JoshuaMularczyk/Software_Defined_Radio_Receiver/Visuals/Arduino and Si5351.jpg

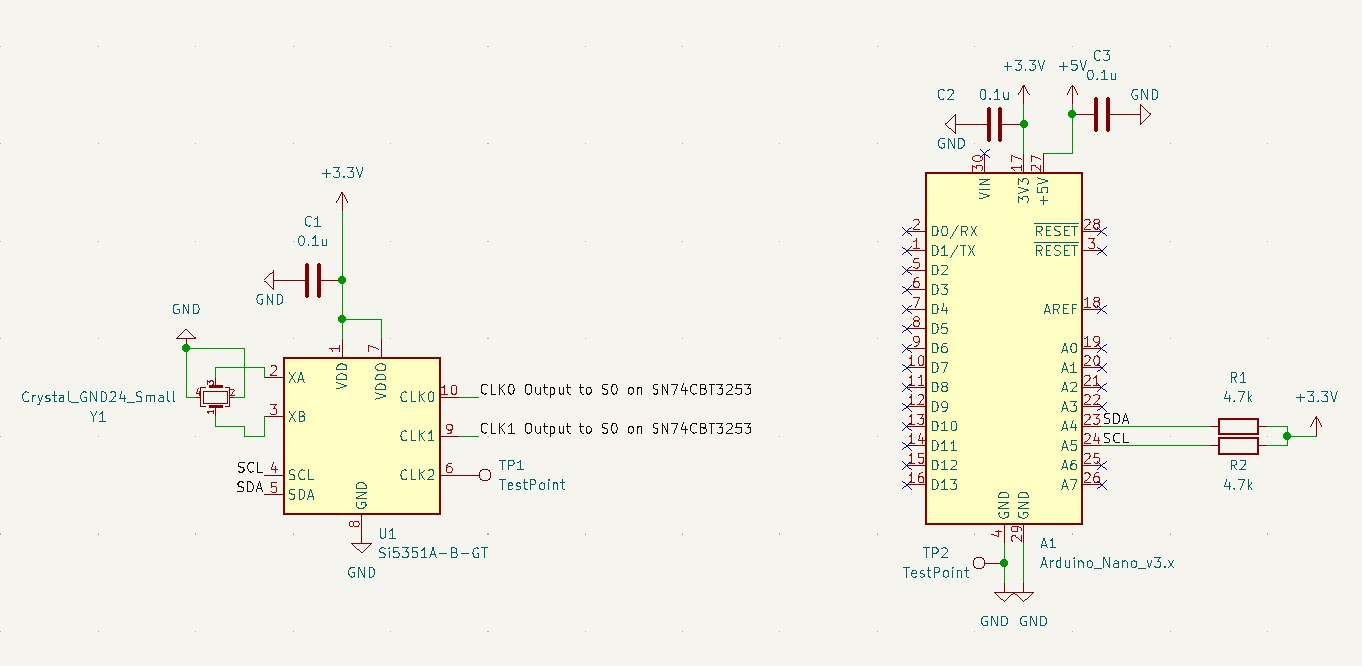
Visuals/Arduino and Si5351.jpg
