JoshuaMularczyk/Software_Defined_Radio_Receiver/Visuals/BandPass Filter and Voltage Divider.jpg

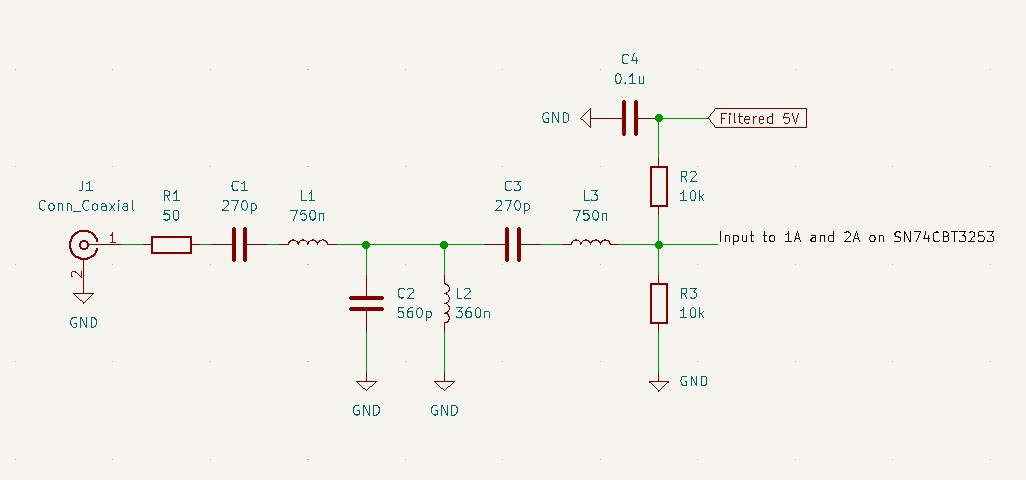
Visuals/BandPass Filter and Voltage Divider.jpg
