JoshuaMularczyk/Software_Defined_Radio_Receiver/Visuals/Bandpass Filter Simulation Graph.jpg

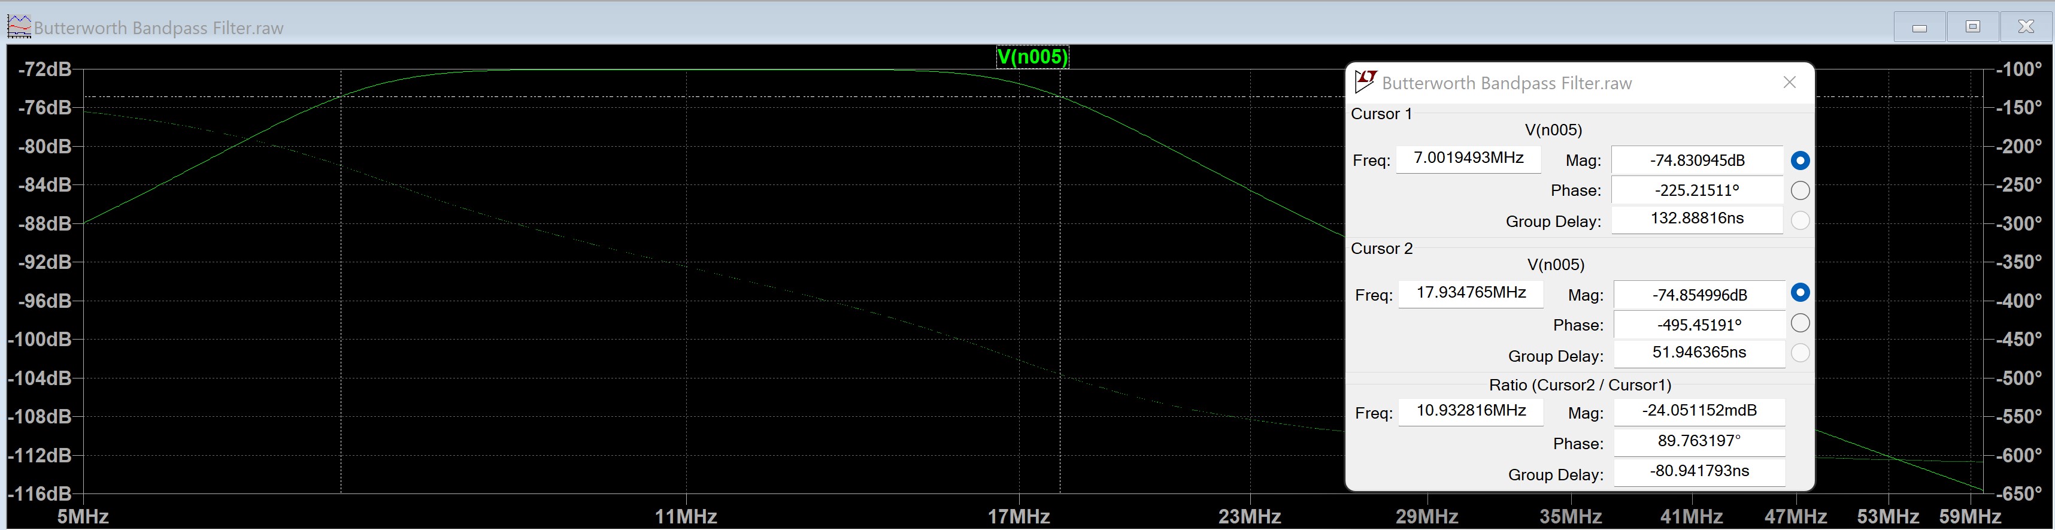
Visuals/Bandpass Filter Simulation Graph.jpg
