JoshuaMularczyk/Software_Defined_Radio_Receiver/Visuals/Bandpass Filter Simulation.jpg

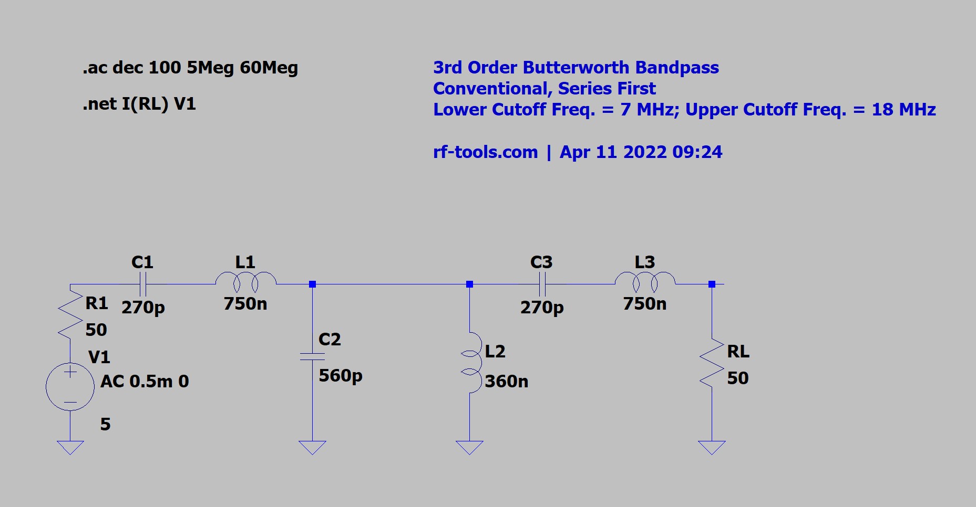
Visuals/Bandpass Filter Simulation.jpg
