JoshuaMularczyk/Software_Defined_Radio_Receiver/Visuals/blockdia.PNG

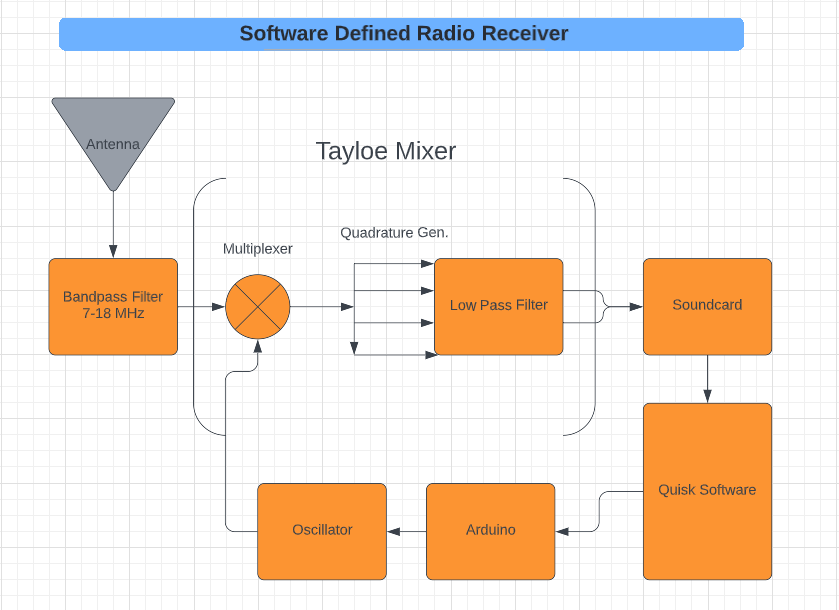
Visuals/blockdia.PNG
