JoshuaMularczyk/Software_Defined_Radio_Receiver/Visuals/IMG-2087.jpg

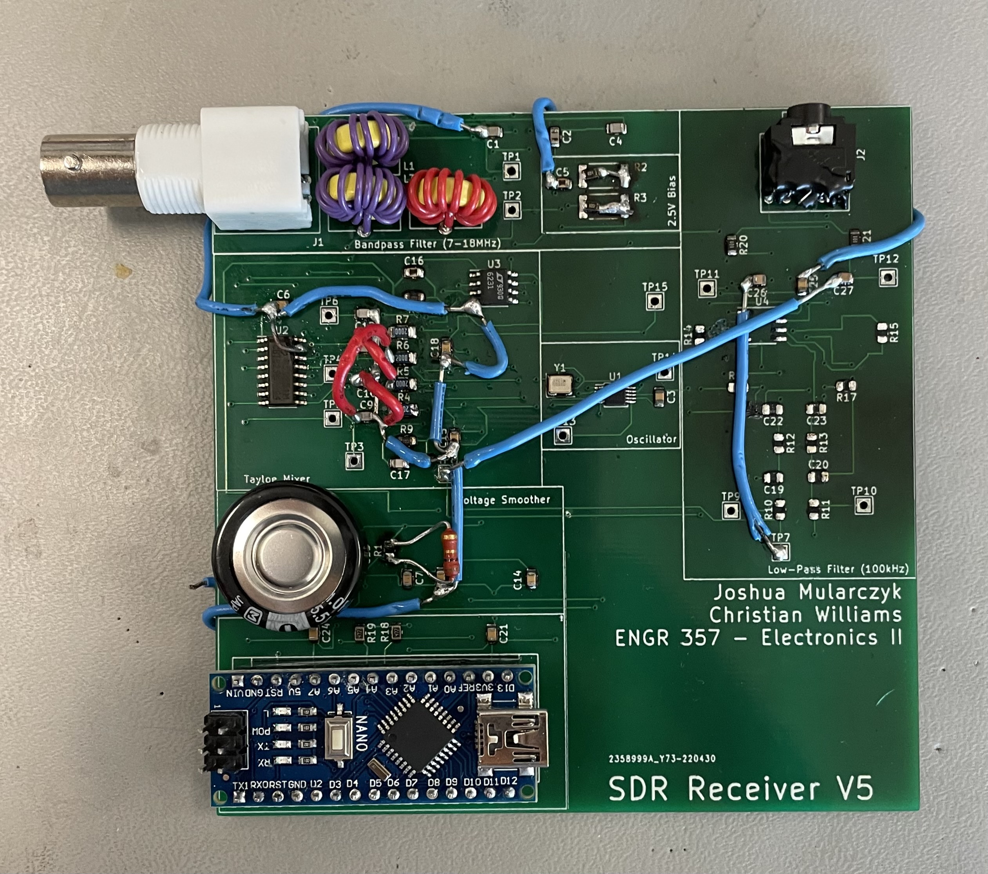
Visuals/IMG-2087.jpg
