JoshuaMularczyk/Software_Defined_Radio_Receiver/Visuals/IMG-2090.jpg

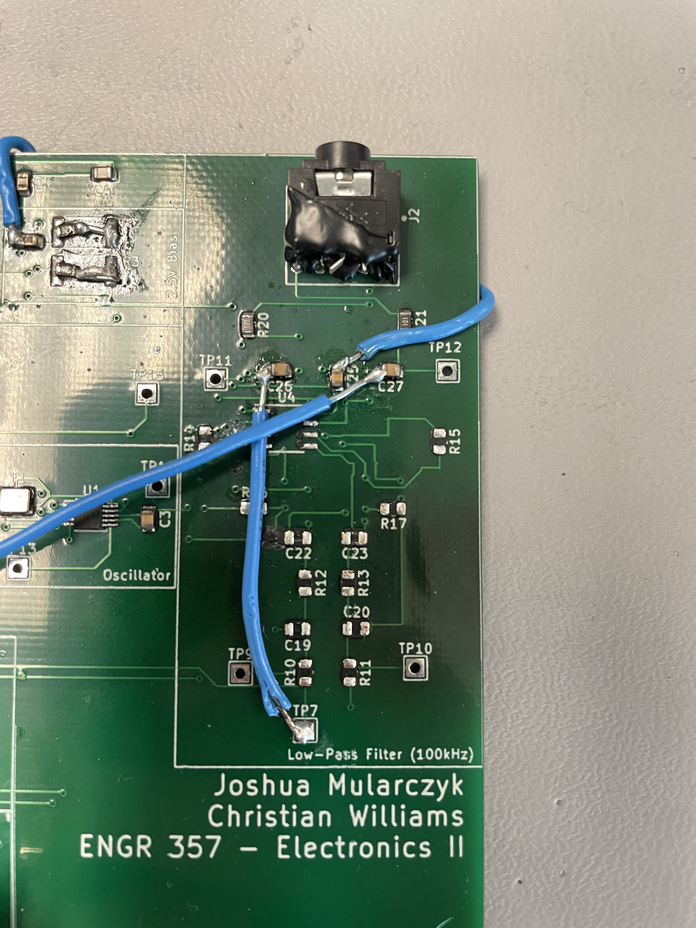
Visuals/IMG-2090.jpg
