JoshuaMularczyk/Software_Defined_Radio_Receiver/Visuals/listeningIn.png

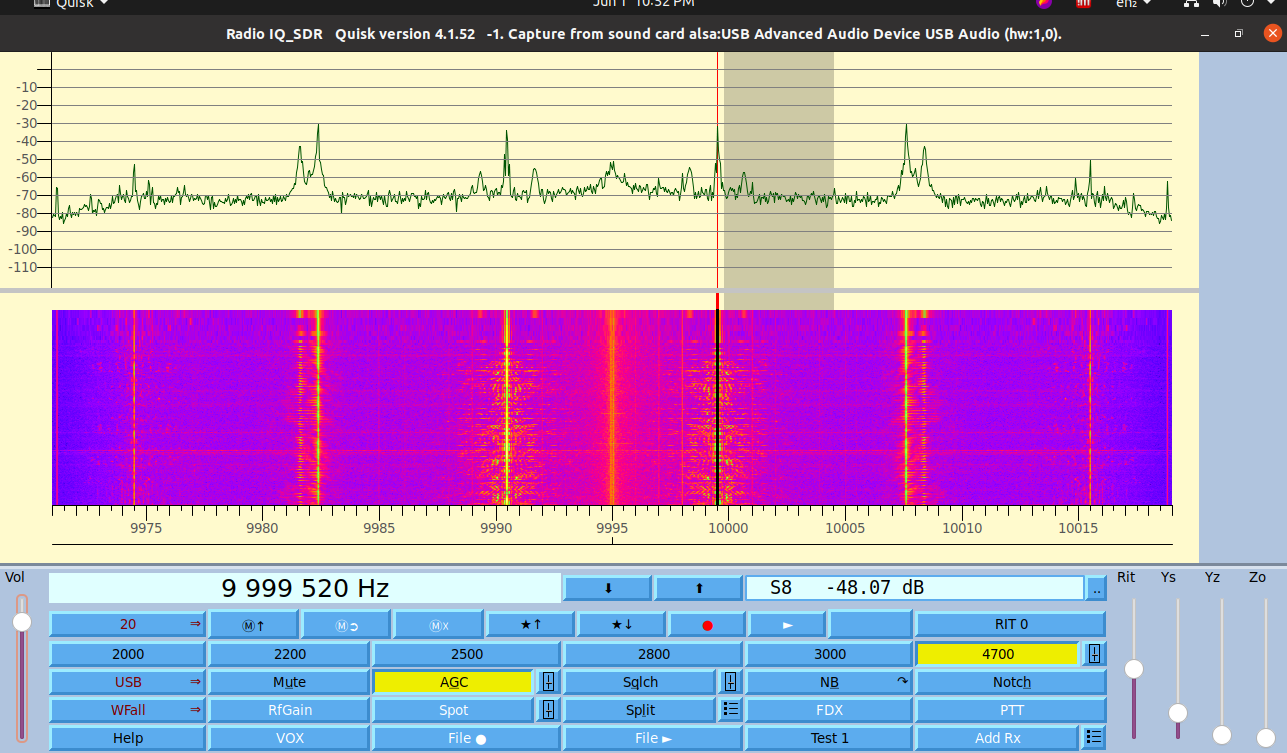
Visuals/listeningIn.png
