JoshuaMularczyk/Software_Defined_Radio_Receiver/Visuals/LowPass Filter Simulation.jpg

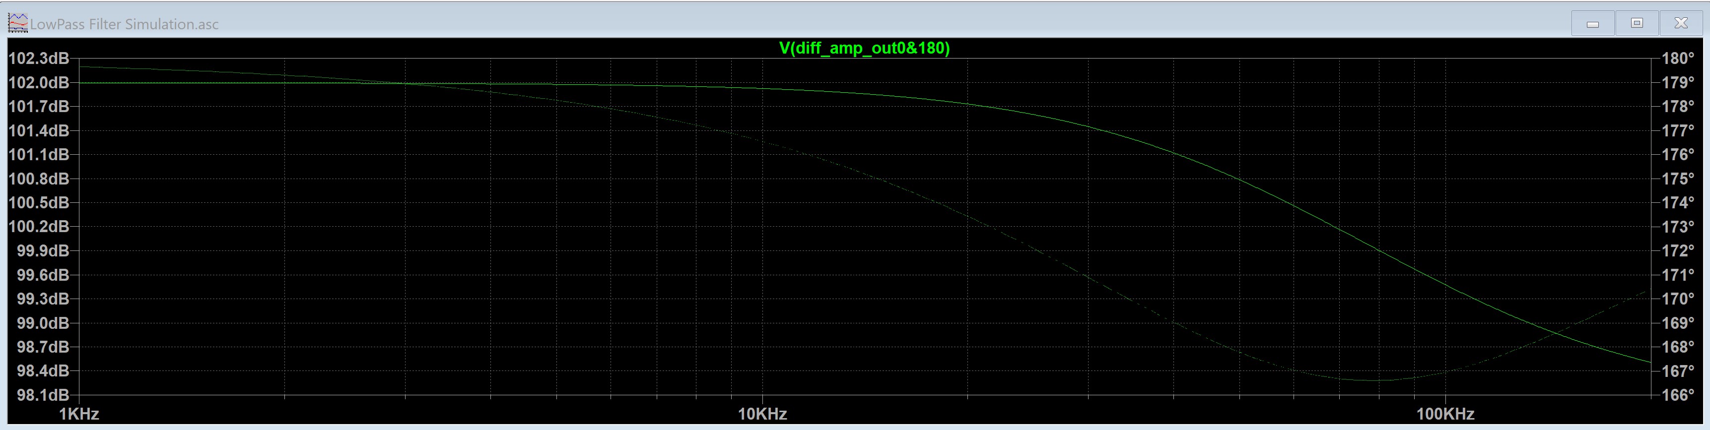
Visuals/LowPass Filter Simulation.jpg
