JoshuaMularczyk/Software_Defined_Radio_Receiver/Visuals/minDec.png

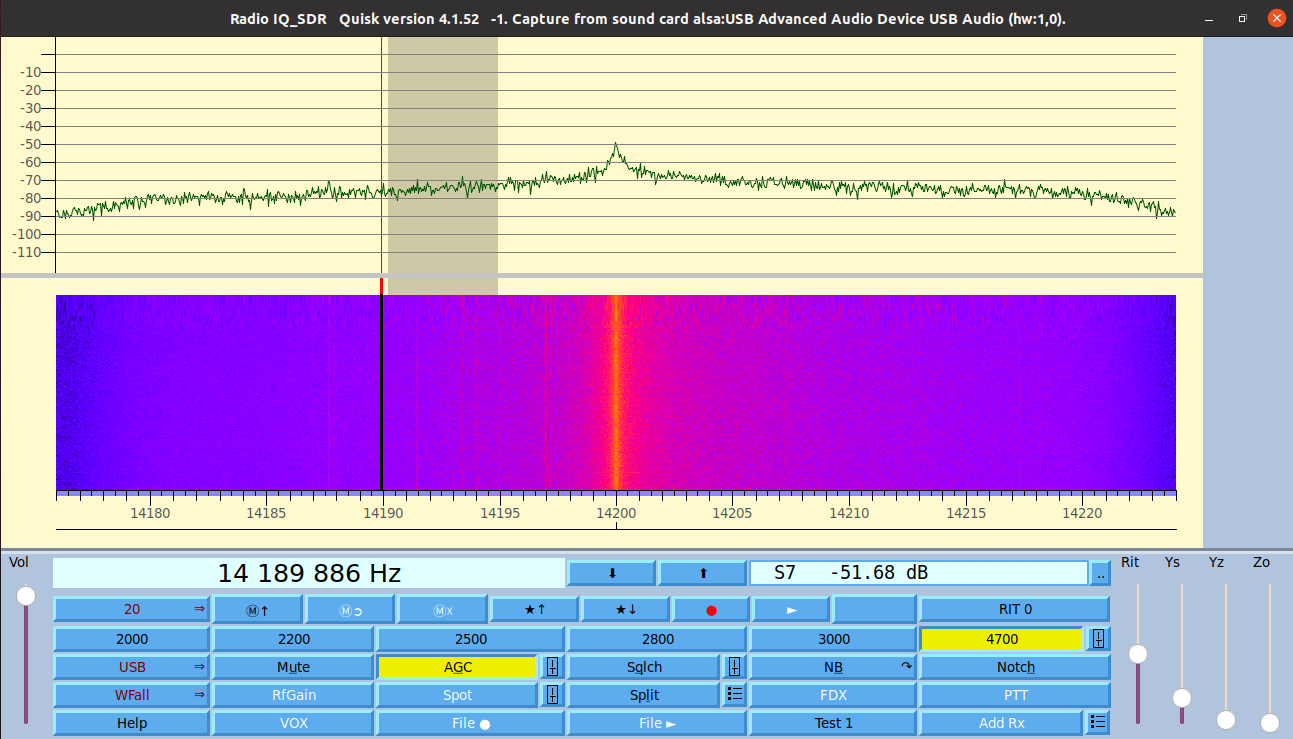
Visuals/minDec.png
