JoshuaMularczyk/Software_Defined_Radio_Receiver/Visuals/Tayloe Mixer.jpg

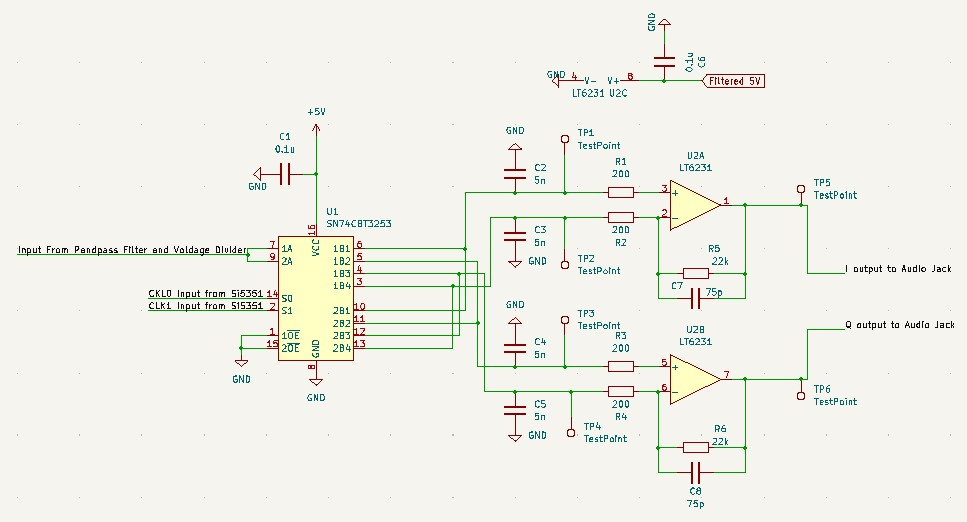
Visuals/Tayloe Mixer.jpg
