JoshuaMularczyk/Software_Defined_Radio_Receiver/Visuals/Voltage Smoother.jpg

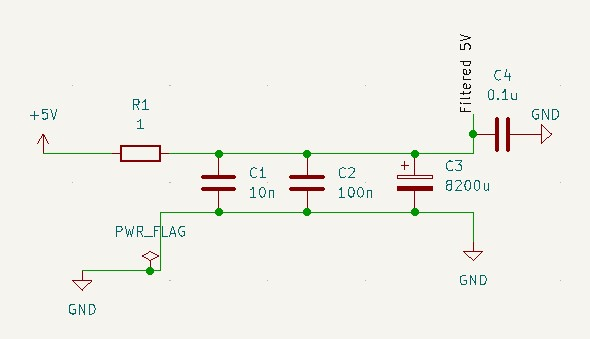
Visuals/Voltage Smoother.jpg
