JoshuaMularczyk/Software_Defined_Radio_Receiver/Visuals/weather.png

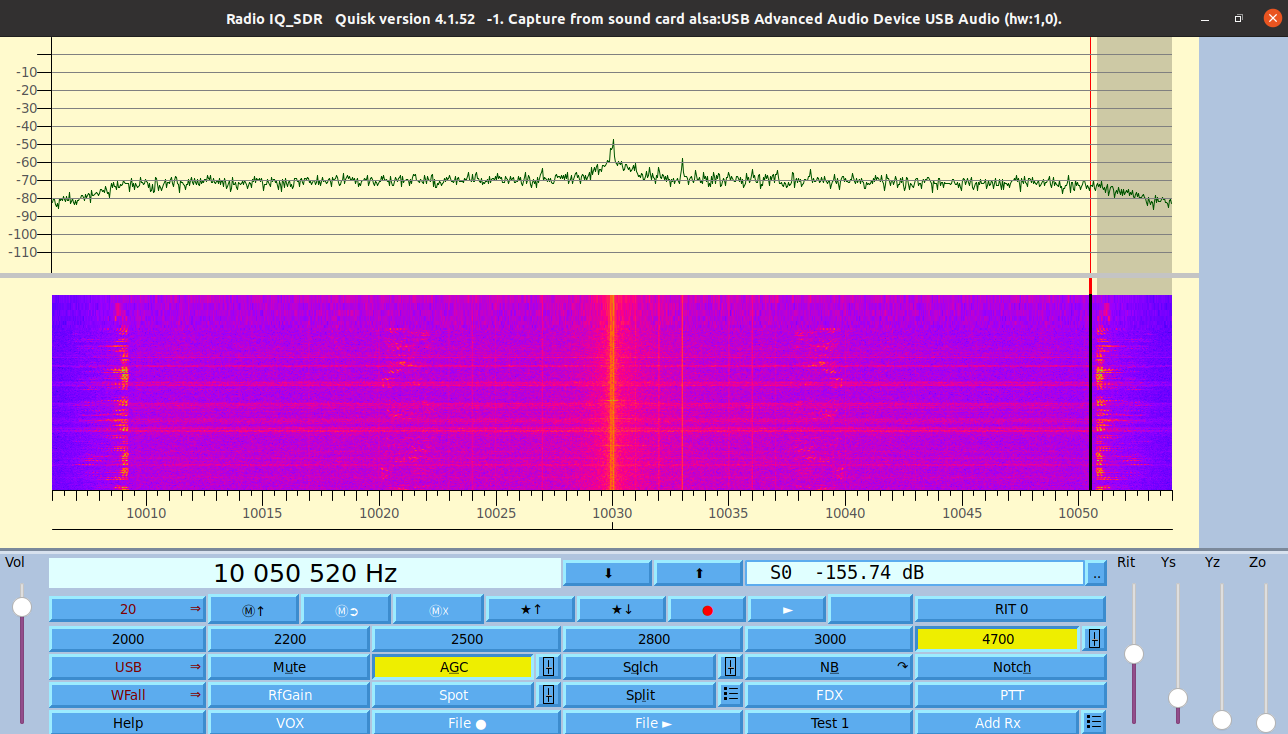
Visuals/weather.png
