JoshuaMularczyk/Software_Defined_Radio_Receiver/Simulations/Butterworth Bandpass Filter.asc

C1: cap; 270p
C2: cap; 560p
C3: cap; 270p
L1: ind; 750n
L2: ind; 360n
L3: ind; 750n
R1: res; 50
RL: res; 50
V1: voltage; 5; AC 0.5m 0
Named nets: 0
.ac dec 100 5Meg 60Meg
.net I(RL) V1
3rd Order Butterworth Bandpass
Conventional, Series First
Lower Cutoff Freq. = 7 MHz; Upper Cutoff Freq. = 18 MHz
 

rf-tools.com | Apr 11 2022 09:24
