JoshuaMularczyk/Software_Defined_Radio_Receiver/Simulations/SDRsim v1.asc

C1: cap; 270p
C2: cap; 560p
C3: cap; 270p
C4: cap; 100p
C5: cap; 100p
C6: cap; 100p
C7: cap; 100p
C8: cap; 10n
C9: cap; .1µ
C10: cap; 5n
C11: cap; 5n
C12: cap; 0.1µ
C13: cap; 10n
C14: cap; 5n
C15: cap; 5n
C16: cap; .1µ
L1: ind; 750n
L2: ind; 360n
L3: ind; 750n
R1: res; 50
R2: res; 4.64k
R3: res; 52.3k
R4: res; 4.64k
R5: res; 52.3k
R6: res; 200
R7: res; 200
R8: res; 10k
R9: res; 10k
R10: res; 10k
R11: res; 200
R12: res; 200
R13: res; 10k
R14: res; 50
R15: res; 50
R16: res; 50
R17: res; 50
R18: res; 55k
R19: res; 55k
R20: res; 17.4k
R21: res; 2.49k
R22: res; 17.4k
R23: res; 2.49k
S1: sw
S2: sw
S3: sw
S4: sw
U1: LT6231
U2: LT6231
U3: LT6231
U4: LT6231
V1: voltage; SINE(0 .5m {RF_frequency})
V2: voltage; 5
V3: voltage; PULSE(0 1 {switch_time} 0.001p 0.001p {switch_time} {4*switch_time})
V4: voltage; PULSE(0 1 {2*switch_time} 0.001p 0.001p {switch_time} {4*switch_time})
V5: voltage; PULSE(0 1 {3*switch_time} 0.001p 0.001p {switch_time} {4*switch_time})
V6: voltage; PULSE(0 1 0 0.001p 0.001p {switch_time} {4*switch_time})
V7: voltage; -5
Named nets: 0, Filter_RF_Signal, Filtered_5V, 0_degrees, 90_degrees, 180_degrees, 270_degrees, Negative_Vcc_after, Vout_0, Vout_90, Vout_180, Vout_270, Negative_Filtered_5V, Vcc_after, Diff_Amp_Out_90&270, Diff_Amp_Out0&180
;ac dec 100 1k 150k
.model SW SW(Vt=0.9 Vh=0 Ron=1 Roff=100G)
.param RF_frequency=11Meg LO_freq={RF_frequency - 10.7k} LO_period={1/LO_freq} LOB_delay={LOA_delay*2} LOA_delay={LO_on/2} LO_on={LO_period/2} switch_time={LO_period/4}
.tran 0 100m 0
.tran 0 1u 0 0.001u
We ended up removing this pair of lowpass filters because we had a really good signal
output from the first pair of lowpass filters.
Low Pass FIlter For I and Q signals
Band Pass FIlter
Tayloe Mixer
Si5351 Clock Generation
